hb020/ersaswitch/images/IMG_2193.jpg

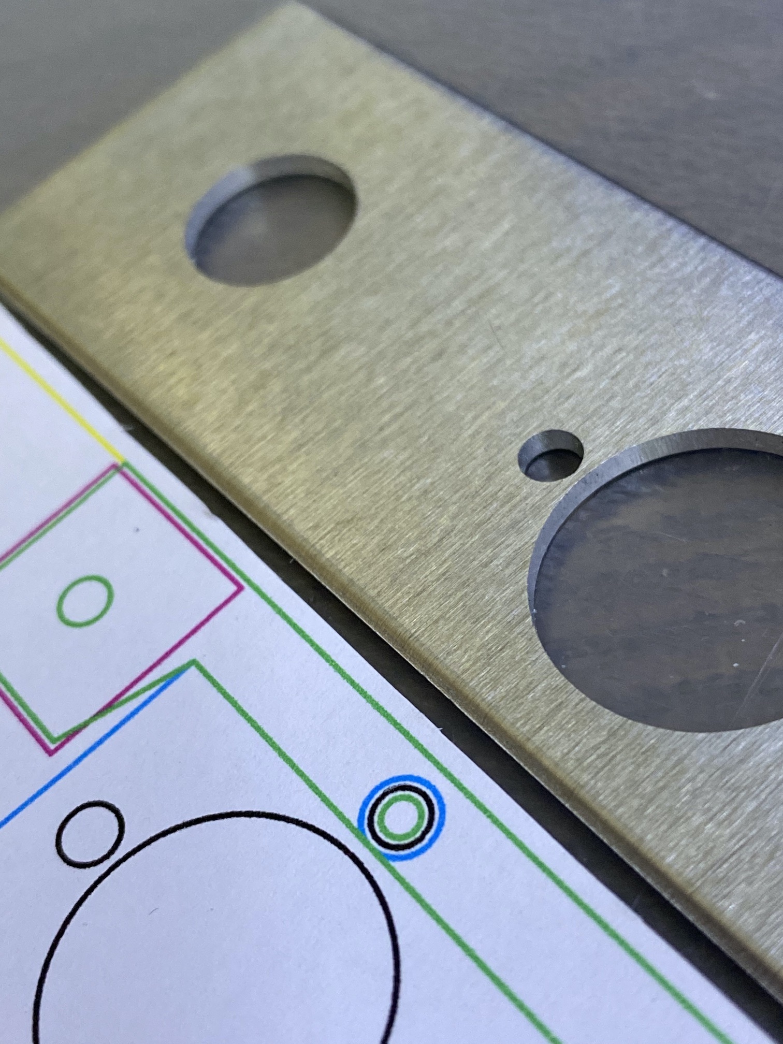
images/IMG_2193.jpg
