hb020/ersaswitch/images/IMG_2194.jpg

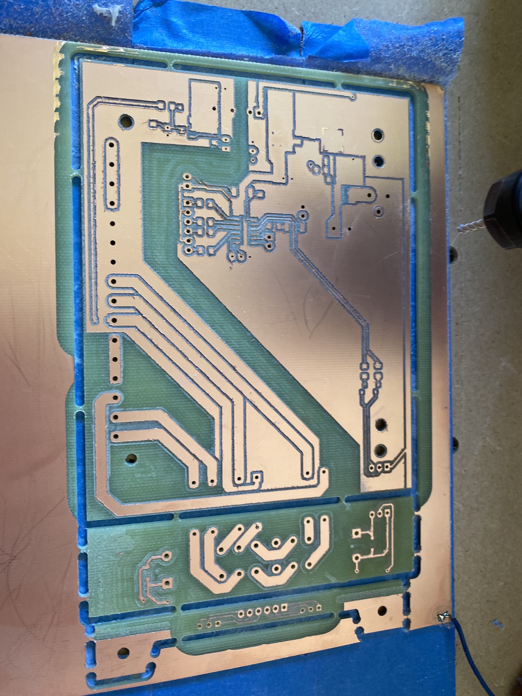
images/IMG_2194.jpg
