hb020/ersaswitch/images/IMG_2195.jpg

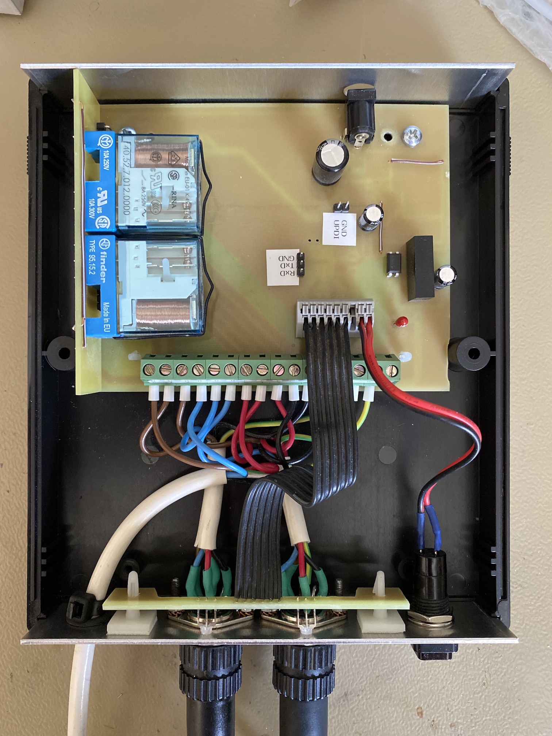
images/IMG_2195.jpg
