hb020/ersaswitch/images/IMG_2200.jpg

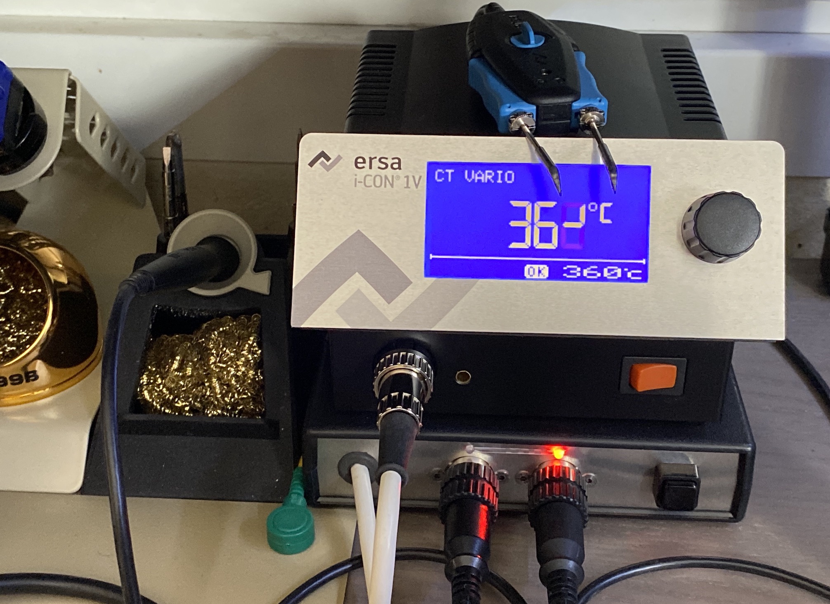
images/IMG_2200.jpg
